universam1/iSpindel/drawer/mwx-Edition/mwx-Edition.jpg

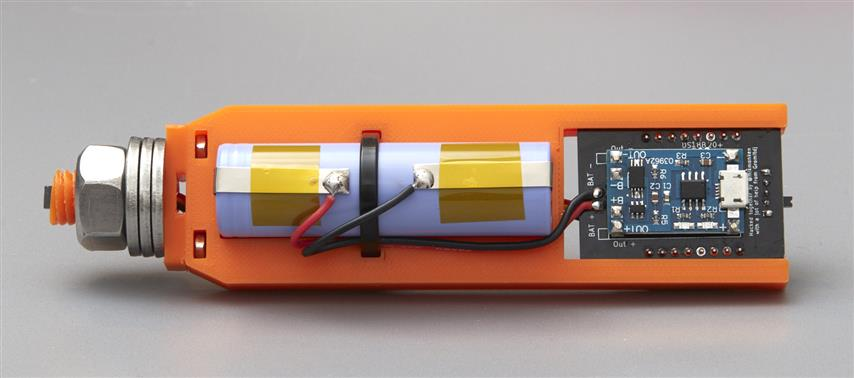
drawer/mwx-Edition/mwx-Edition.jpg
