universam1/iSpindel/pics/PCB/12-GY521Vorbereitung.JPG

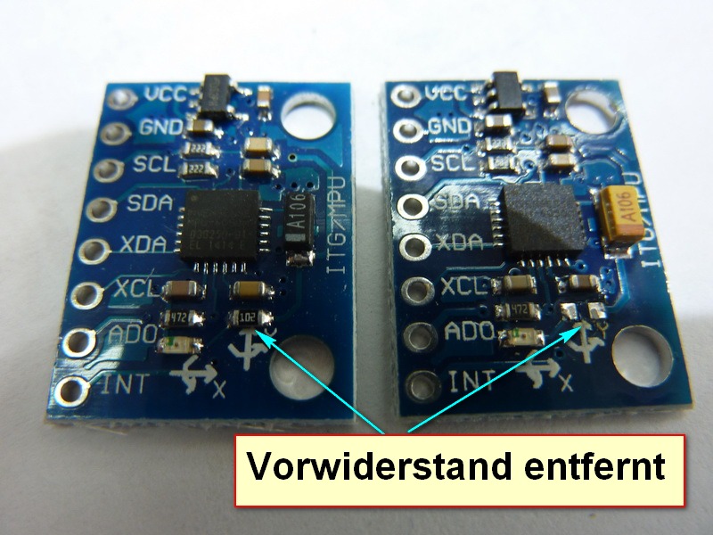
pics/PCB/12-GY521Vorbereitung.JPG
