universam1/iSpindel/pics/UbiDS.jpg

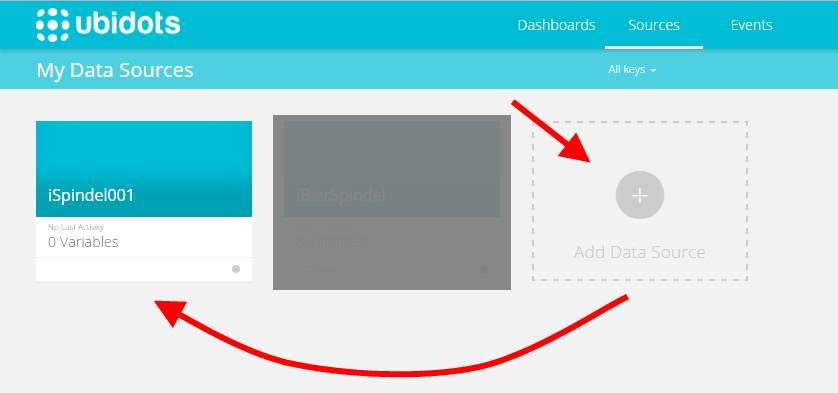
pics/UbiDS.jpg
