universam1/iSpindel/pics/UbiIDs.jpg

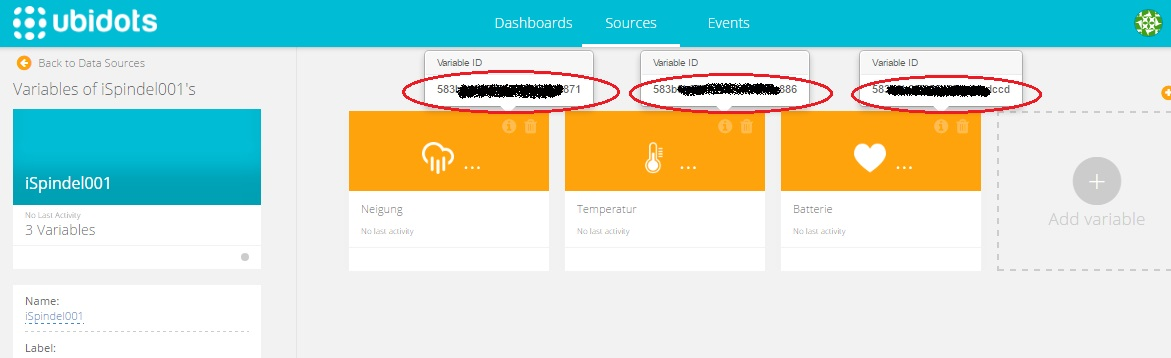
pics/UbiIDs.jpg
