universam1/iSpindel/pics/Calibration_Sheet_EN.PNG

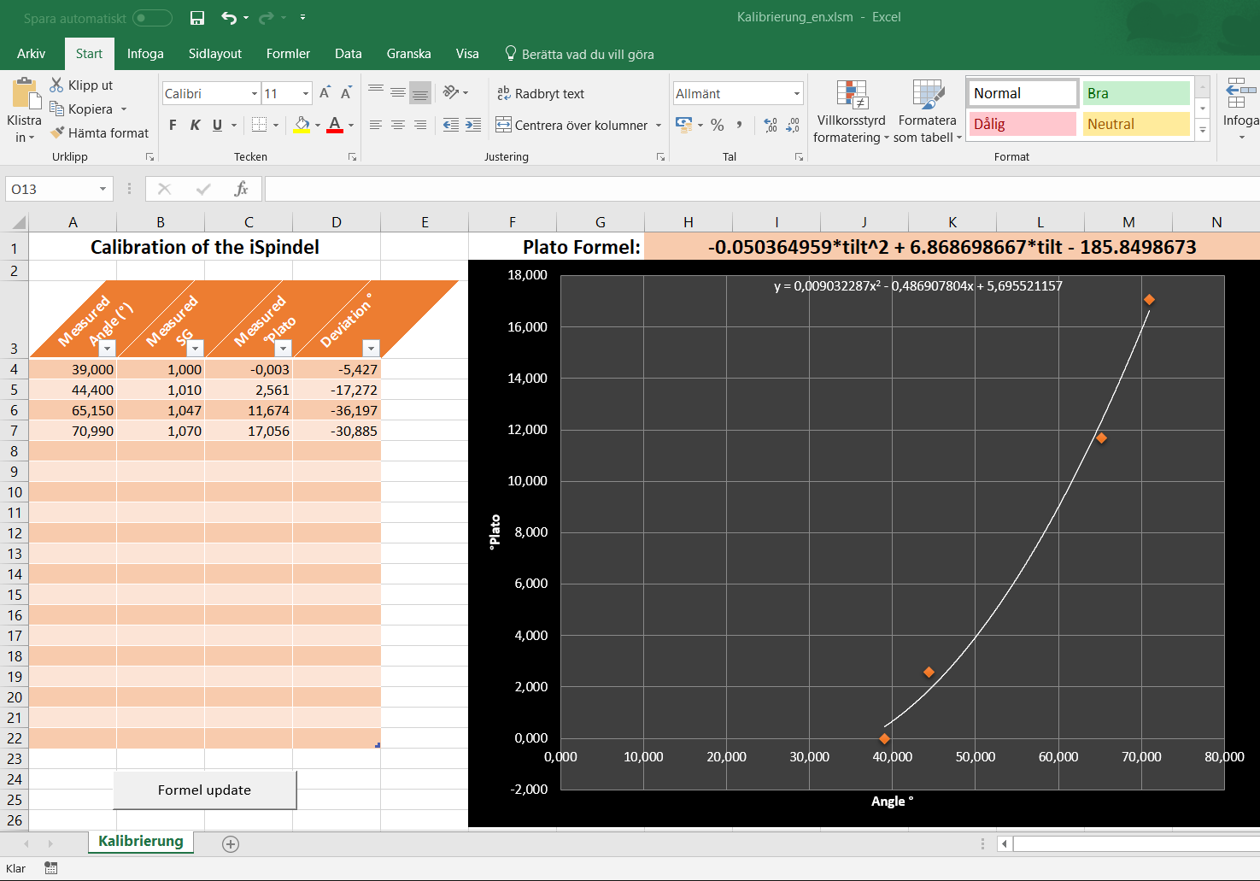
pics/Calibration_Sheet_EN.PNG
