universam1/iSpindel/iSpindel/WiFiManagerKT.h

/**************************************************************
   WiFiManager is a library for the ESP8266/Arduino platform
   (https://github.com/esp8266/Arduino) to enable easy
   configuration and reconfiguration of WiFi credentials using a Captive Portal
   inspired by:
   http://www.esp8266.com/viewtopic.php?f=29&t=2520
   https://github.com/chriscook8/esp-arduino-apboot
   https://github.com/esp8266/Arduino/tree/esp8266/hardware/esp8266com/esp8266/libraries/DNSServer/examples/CaptivePortalAdvanced
   This version built by Ken Taylor https://github.com/kentaylor
   Licensed under MIT license
 **************************************************************/

#ifndef WiFiManager_h
#define WiFiManager_h

#include "Globals.h"
#include <ESP8266WiFi.h>
#include <ESP8266WebServer.h>
#include <DNSServer.h>
#include <memory>
#undef min
#undef max
#include <algorithm>
extern "C" {
  #include "user_interface.h"
}

#define WFM_LABEL_BEFORE 1
#define WFM_LABEL_AFTER 2
#define WFM_NO_LABEL 0

const char HTTP_ISPINDEL_IMG[] PROGMEM = "<img src=\"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" style=\"padding: 40px; display: block; width: 80%;\"/>";

const char HTTP_200[] PROGMEM = "HTTP/1.1 200 OK\r\nContent-Type: text/html\r\n\r\n";
const char HTTP_HEAD[] PROGMEM = "<!DOCTYPE html><html lang=\"en\"><head><meta name=\"viewport\" content=\"width=device-width, initial-scale=1, user-scalable=no\"/><title>{v}</title>";

const char HTTP_STYLE[] PROGMEM = "<style>body,textarea,input,select{background: 0;border-radius: 0;font: 16px sans-serif;margin: 0}textarea,input,select{outline: 0;font-size: 14px;border: 1px solid #ccc;padding: 8px;width: 90%}.btn a{text-decoration: none}.container{margin: auto;width: 90%}@media(min-width:1200px){.container{margin: auto;width: 30%}}@media(min-width:768px) and (max-width:1200px){.container{margin: auto;width: 50%}}.btn,h2{font-size: 2em}h1{font-size: 3em}.btn{background: #0ae;border-radius: 4px;border: 0;color: #fff;cursor: pointer;display: inline-block;margin: 2px 0;padding: 10px 14px 11px;width: 100%}.btn:hover{background: #09d}.btn:active,.btn:focus{background: #08b}label>*{display: inline}form>*{display: block;margin-bottom: 10px}textarea:focus,input:focus,select:focus{border-color: #5ab}.msg{background: #def;border-left: 5px solid #59d;padding: 1.5em}.q{float: right;width: 64px;text-align: right}.l{background: url('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') no-repeat left center;background-size: 1em}input[type='checkbox']{float: left;width: 20px}.table td{padding:.5em;text-align:left}.table tbody>:nth-child(2n-1){background:#ddd}</style>";

const char HTTP_SCRIPT[] PROGMEM = R"V0G0N(<script>
var $ = function(id) { return document.getElementById(id);};
var labels = document.getElementsByTagName('LABEL');
function set(id, show){
  $(id).style.display = show ? 'block':'none';
  $(id).label.style.display = show ? 'block':'none';}
function c(l){s.value=l.innerText||l.textContent;p.focus();}
function sAPI(){
	var sel = $('API').options[$('API').selectedIndex].textContent;
	$('selAPI').value = parseInt($('API').options[$('API').selectedIndex].value);
switch(sel) {
case "Ubidots":
	set('token',1);
	set('server',0);
	set('url',0);
	set('port',0);
  break;
case "CraftBeerPi":
  set('url',0);
  set('port',0);
	set('token',0);
	set('server',1);
  break;
case "HTTP":
  set('url',1);
  set('port',1);
	set('token',0);
	set('server',1);
  break;
case "TControl":
  set('server',1);
  set('port',0);
  set('token',0);
  set('url',0);
  break;
case "FHEM":
  set('server',1);
  set('port',1);
  set('token',0);
  set('url',0);
  break;
case "TCP":
  set('server',1);
  set('port',1);
  set('token',0);
  set('url',0);
  break;
}};
window.onload = function(e){ 
 for (var i = 0; i < labels.length; i++) {
 if (labels[i].htmlFor != '') {
 var elem = $(labels[i].htmlFor);
 if (elem) elem.label = labels[i]; }}
  $('API').value = $('selAPI').value; sAPI();};
</script>)V0G0N";


const char HTTP_API_LIST[] PROGMEM = R"V0G0N(
<select id="API" onclick="sAPI()">
<option value=0>Ubidots</option>
<option value=2>CraftBeerPi</option>
<option value=3>HTTP</option>
<option value=4>TControl</option>
<option value=5>FHEM</option>
<option value=6>TCP</option>
</select>)V0G0N";

const char TYPE_HIDDEN[]  = "type=\"hidden\"";
const char TYPE_NUMBER[]  = "type=\"number\" step=\"any\"";

const char HTTP_HEAD_END[] PROGMEM        = "</head><body><div class=\"container\">";
const char HTTP_PORTAL_OPTIONS[] PROGMEM  = "<form action=\"/iSpindel\" method=\"get\"><button class=\"btn\">iSpindel Info</button></form><br/><form action=\"/wifi\" method=\"get\"><button class=\"btn\">Configuration</button></form><br/><form action=\"/mnt\" method=\"get\"><button class=\"btn\">Maintenance</button></form><br/><form action=\"/i\" method=\"get\"><button class=\"btn\">Information</button></form><br/><form action=\"/close\" method=\"get\"><button class=\"btn\">Exit Portal</button></form><br/>";
const char HTTP_ITEM[] PROGMEM            = "<div><a href=\"#p\" onclick=\"c(this)\">{v}</a>&nbsp;<span class=\"q {i}\">{r}%</span></div>";
const char JSON_ITEM[] PROGMEM            = "{\"SSID\":\"{v}\", \"Encryption\":{i}, \"Quality\":\"{r}\"}";
const char HTTP_FORM_START[] PROGMEM      = "<form method=\"get\" action=\"wifisave\"><label>SSID</label><input id=\"s\" name=\"s\" length=32 placeholder=\"SSID\"><label>Password</label><input id=\"p\" name=\"p\" length=64 placeholder=\"password\">";
const char HTTP_FORM_LABEL[] PROGMEM      = "<label for=\"{i}\">{p}</label>";
const char HTTP_FORM_PARAM[] PROGMEM      = "<input id=\"{i}\" name=\"{n}\" length={l} placeholder=\"{p}\" value=\"{v}\" {c}>";
const char HTTP_FORM_END[] PROGMEM        = "<button class=\"btn\" type=\"submit\">save</button></form>";
const char HTTP_SAVED[] PROGMEM           = "<div class=\"msg\"><strong>Credentials Saved</strong><br>Trying to connect ESP to the {x} network.<br>Give it 10 seconds or so and check <a href=\"/\">how it went.</a> <p/>The {v} you are connected to will be restarted on the radio channel of the {x} network and continue in normal mode thus not being accessible until manually resetted to configuration mode.";
const char HTTP_END[] PROGMEM             = "</div></body></html>";
const char HTTP_UPDATE_FAI[] PROGMEM = "Update Failed!";
const char HTTP_UPDATE_SUC[] PROGMEM = "Update Success! Rebooting...";

#define WIFI_MANAGER_MAX_PARAMS 14

class WiFiManagerParameter {
  public:
    WiFiManagerParameter(const char *custom);
    WiFiManagerParameter(const char *id, const char *placeholder, const char *defaultValue, int length);
    WiFiManagerParameter(const char *id, const char *placeholder, const char *defaultValue, int length, const char *custom);
    WiFiManagerParameter(const char *id, const char *placeholder, const char *defaultValue, int length, const char *custom, int labelPlacement);

    const char *getID();
    const char *getValue();
    const char *getPlaceholder();
    int         getValueLength();
    int         getLabelPlacement();
    const char *getCustomHTML();
  private:
    const char *_id;
    const char *_placeholder;
    char       *_value;
    int         _length;
	int         _labelPlacement;
    const char *_customHTML;

    void init(const char *id, const char *placeholder, const char *defaultValue, int length, const char *custom, int labelPlacement);

    friend class WiFiManager;
};


class WiFiManager
{
  public:
    WiFiManager();
    ~WiFiManager();

    boolean       autoConnect(); //Deprecated. Do not use.
    boolean       autoConnect(char const *apName, char const *apPassword = NULL); //Deprecated. Do not use.

    //if you want to start the config portal
    boolean       startConfigPortal();
    boolean       startConfigPortal(char const *apName, char const *apPassword = NULL);

    // get the AP name of the config portal, so it can be used in the callback
    String        getConfigPortalSSID();

    void          resetSettings();

    //sets timeout before webserver loop ends and exits even if there has been no setup.
    //usefully for devices that failed to connect at some point and got stuck in a webserver loop
    //in seconds setConfigPortalTimeout is a new name for setTimeout
    void          setConfigPortalTimeout(unsigned long seconds);
    void          setTimeout(unsigned long seconds);

    //sets timeout for which to attempt connecting, usefull if you get a lot of failed connects
    void          setConnectTimeout(unsigned long seconds);


    void          setDebugOutput(boolean debug);
    //defaults to not showing anything under 8% signal quality if called
    void          setMinimumSignalQuality(int quality = 8);
    //sets a custom ip /gateway /subnet configuration
    void          setAPStaticIPConfig(IPAddress ip, IPAddress gw, IPAddress sn);
    //sets config for a static IP
    void          setSTAStaticIPConfig(IPAddress ip, IPAddress gw, IPAddress sn);
    //called when AP mode and config portal is started
    void          setAPCallback( void (*func)(WiFiManager*) );
    //called when settings have been changed and connection was successful
    void          setSaveConfigCallback( void (*func)(void) );
    //adds a custom parameter
    void          addParameter(WiFiManagerParameter *p);
    //if this is set, it will exit after config, even if connection is unsucessful.
    void          setBreakAfterConfig(boolean shouldBreak);
    //if this is set, try WPS setup when starting (this will delay config portal for up to 2 mins)
    //TODO
    //if this is set, customise style
    void          setCustomHeadElement(const char* element);
    //if this is true, remove duplicated Access Points - defaut true
    void          setRemoveDuplicateAPs(boolean removeDuplicates);
    //Scan for WiFiNetworks in range and sort by signal strength
    //space for indices array allocated on the heap and should be freed when no longer required
    int           scanWifiNetworks(int **indicesptr);

  private:
    std::unique_ptr<DNSServer>        dnsServer;
    std::unique_ptr<ESP8266WebServer> server;

    //const int     WM_DONE                 = 0;
    //const int     WM_WAIT                 = 10;

    //const String  HTTP_HEAD = "<!DOCTYPE html><html lang=\"en\"><head><meta name=\"viewport\" content=\"width=device-width, initial-scale=1\"/><title>{v}</title>";

    void          setupConfigPortal();
    void          startWPS();
    char*         getStatus(int status);

    const char*   _apName                 = "no-net";
    const char*   _apPassword             = NULL;
    String        _ssid                   = "";
    String        _pass                   = "";
    unsigned long _configPortalTimeout    = 0;
    unsigned long _connectTimeout         = 0;
    unsigned long _configPortalStart      = 0;
    /* hostname for mDNS. Set to a valid internet address so that user
    will see an information page if they are connected to the wrong network */
	const char *myHostname = "192.168.4.1";
	int numberOfNetworks;
	int *networkIndices;
    int **networkIndicesptr = &networkIndices;

    IPAddress     _ap_static_ip;
    IPAddress     _ap_static_gw;
    IPAddress     _ap_static_sn;
    IPAddress     _sta_static_ip;
    IPAddress     _sta_static_gw;
    IPAddress     _sta_static_sn;

    int           _paramsCount            = 0;
    int           _minimumQuality         = -1;
    boolean       _removeDuplicateAPs     = true;
    boolean       _shouldBreakAfterConfig = false;
    boolean       _tryWPS                 = false;

    const char*   _customHeadElement      = "";

    //String        getEEPROMString(int start, int len);
    //void          setEEPROMString(int start, int len, String string);

    int           status = WL_IDLE_STATUS;
    int           connectWifi(String ssid, String pass);
    uint8_t       waitForConnectResult();

    void          handleRoot();
    void          handleWifi();
    void          handleWifiSave();
    void          handleServerClose();
    void          handleInfo();
    void          handleiSpindel();
    void          handleState();
    void          handleScan();
    void          handleReset();
    void          handleNotFound();
    void          handleMnt();
    void          handleOffset();
    void          handleUpdating();
    void          handleUpdateDone();
    boolean       captivePortal();
    void          reportStatus(String &page);

    // DNS server
    const byte    DNS_PORT = 53;

    //helpers
    int           getRSSIasQuality(int RSSI);
    boolean       isIp(String str);
    String        toStringIp(IPAddress ip);

    boolean       connect;
    boolean       stopConfigPortal = false;
    boolean       _debug = true;

    void (*_apcallback)(WiFiManager*) = NULL;
    void (*_savecallback)(void) = NULL;

    WiFiManagerParameter* _params[WIFI_MANAGER_MAX_PARAMS];

    template <typename Generic>
    void          DEBUG_WM(Generic text);

    template <class T>
    auto optionalIPFromString(T *obj, const char *s) -> decltype(  obj->fromString(s)  ) {
      return  obj->fromString(s);
    }
    auto optionalIPFromString(...) -> bool {
      DEBUG_WM("NO fromString METHOD ON IPAddress, you need ESP8266 core 2.1.0 or newer for Custom IP configuration to work.");
      return false;
    }
};

#endif
